Trelow/Tsc_Project/Images/1.png

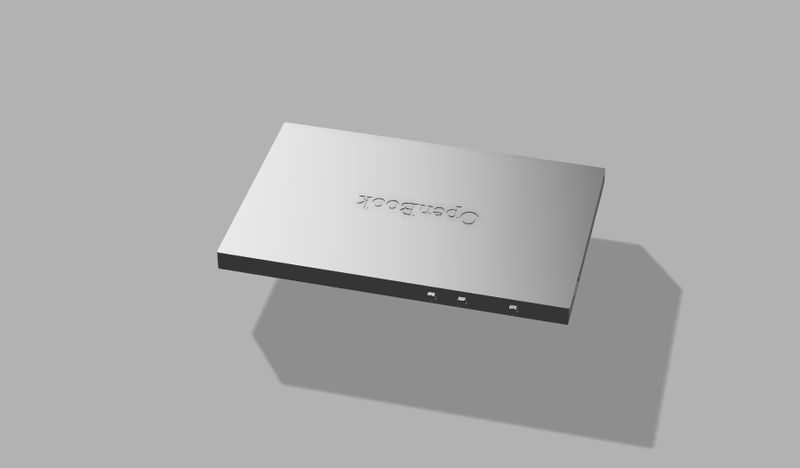
Images/1.png
