Trelow/Tsc_Project/Images/2.png

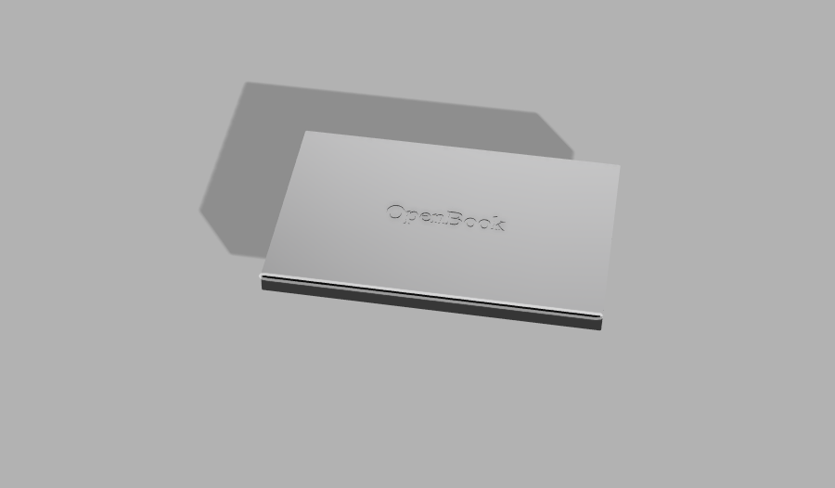
Images/2.png
