Trelow/Tsc_Project/Images/3.png

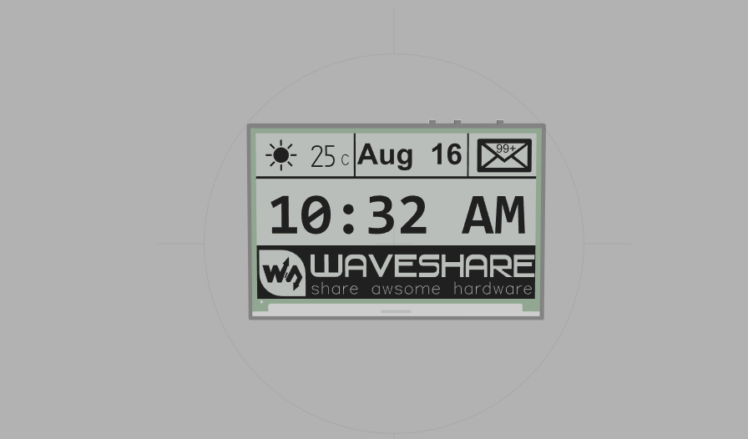
Images/3.png
