Trelow/Tsc_Project/Images/5.png

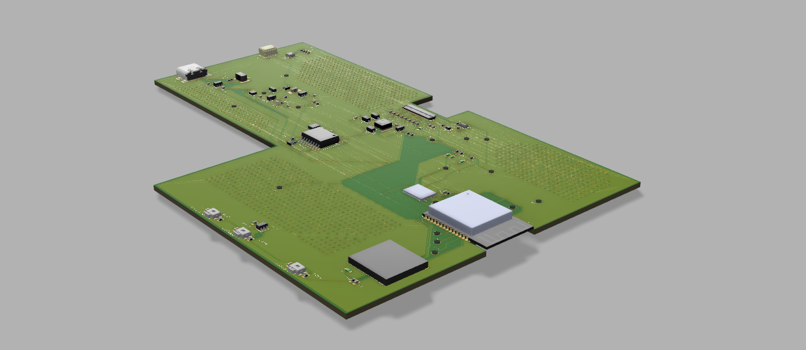
Images/5.png
