Trelow/Tsc_Project/Images/6.png

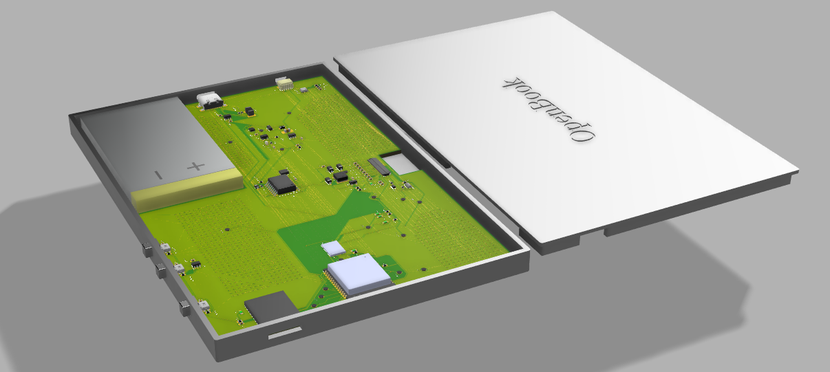
Images/6.png
