Trelow/Tsc_Project/Images/7.png

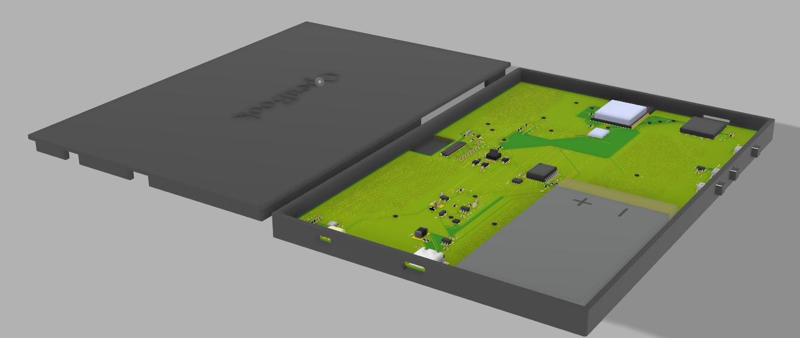
Images/7.png
