Trelow/Tsc_Project/Images/8.png

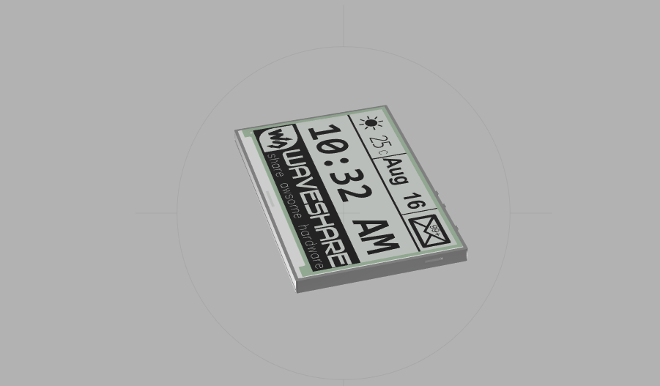
Images/8.png
